plants-are-neat/plants-are-neat.github.io/assets/SerialInit.PNG

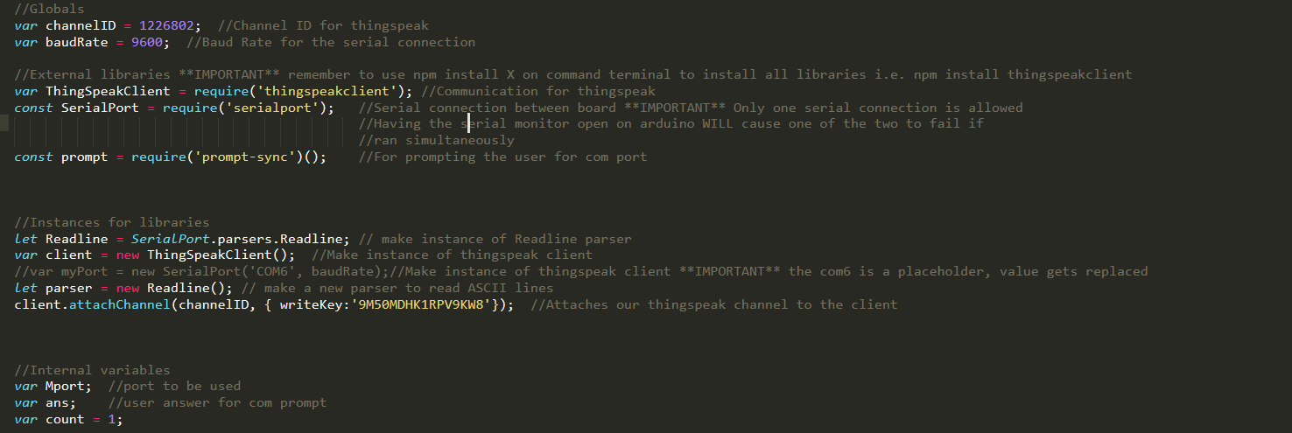
assets/SerialInit.PNG
