plants-are-neat/plants-are-neat.github.io/assets/SerialPrompt.PNG

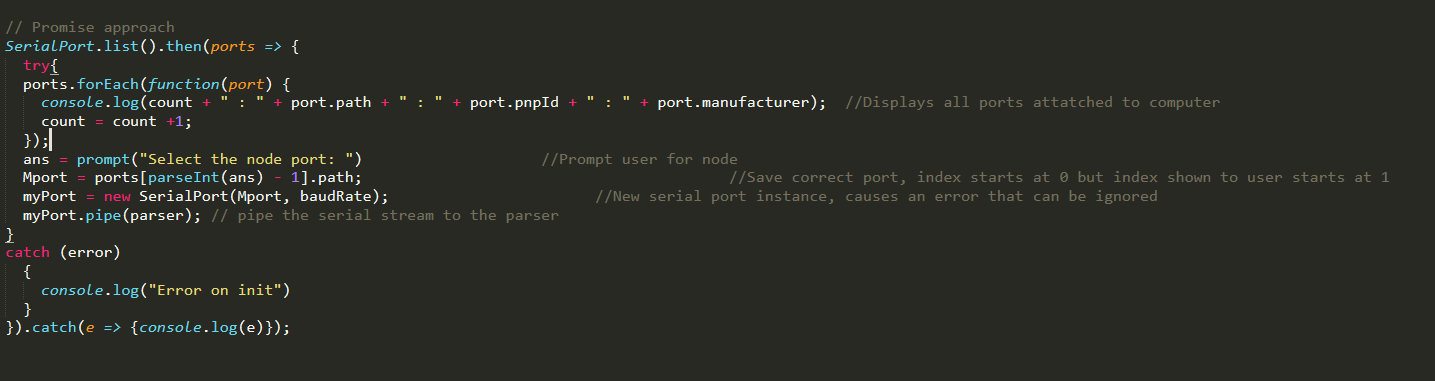
assets/SerialPrompt.PNG
