plants-are-neat/plants-are-neat.github.io/assets/SerialRead.PNG

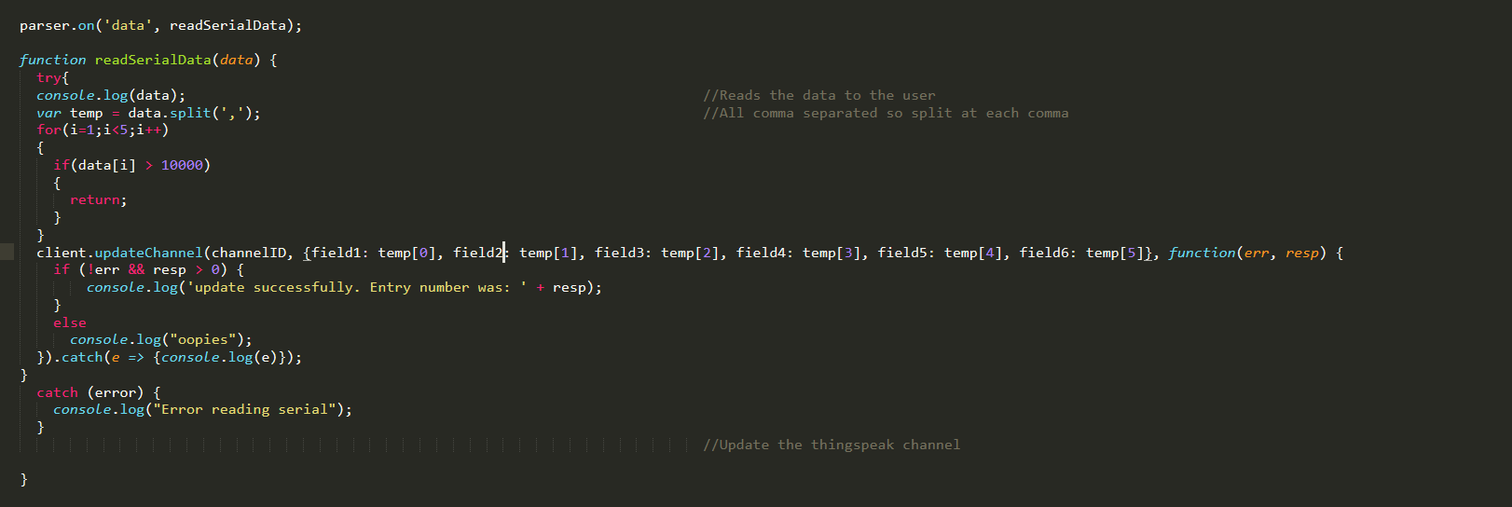
assets/SerialRead.PNG
