plants-are-neat/plants-are-neat.github.io/images/ben.jpg

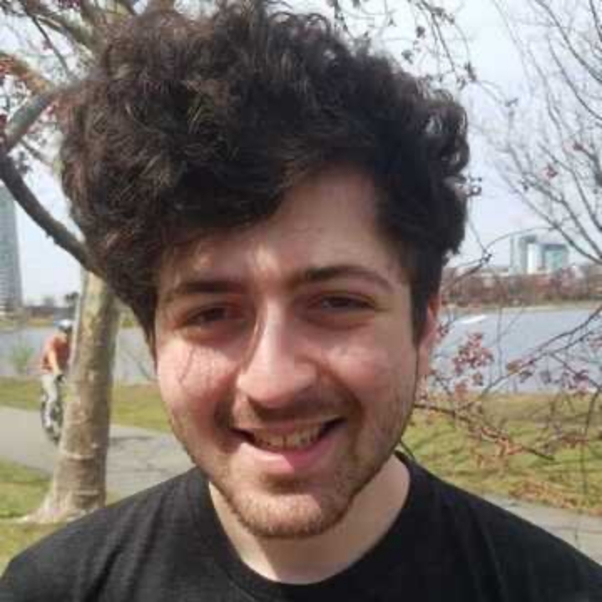
images/ben.jpg
