plants-are-neat/plants-are-neat.github.io/images/img3.jpg

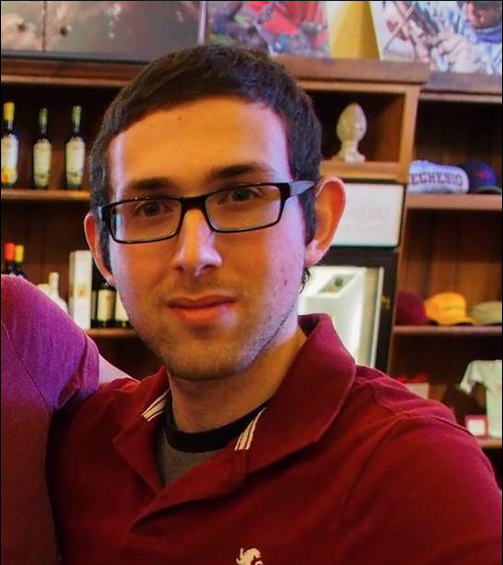
images/img3.jpg
