plants-are-neat/plants-are-neat.github.io/images/img5.jpg

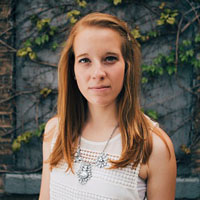
images/img5.jpg
