plants-are-neat/plants-are-neat.github.io/images/maxine.jpg

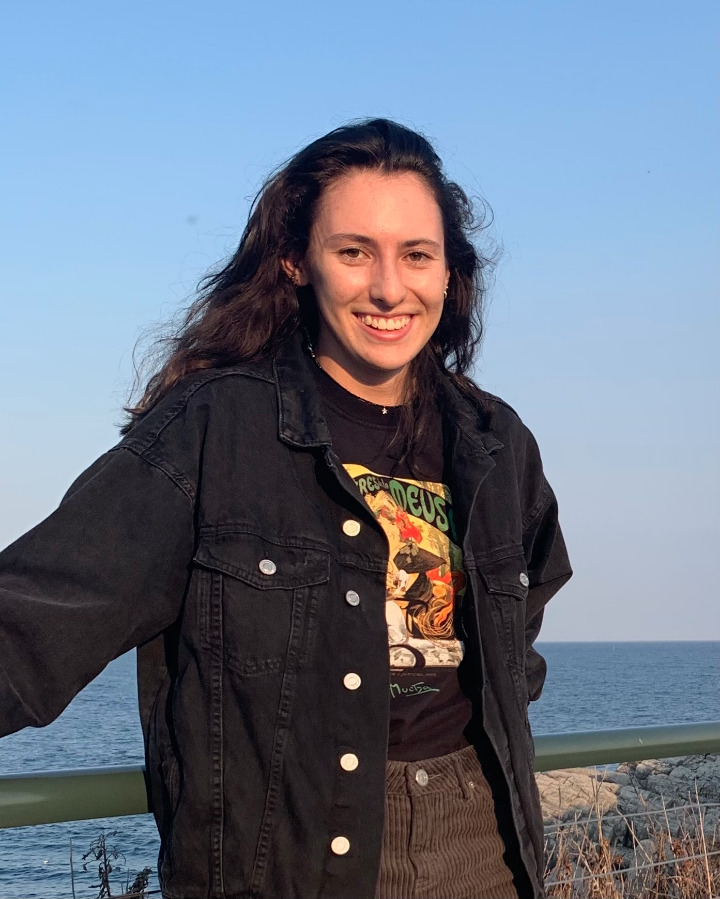
images/maxine.jpg
