plants-are-neat/plants-are-neat.github.io/images/noah.JPG

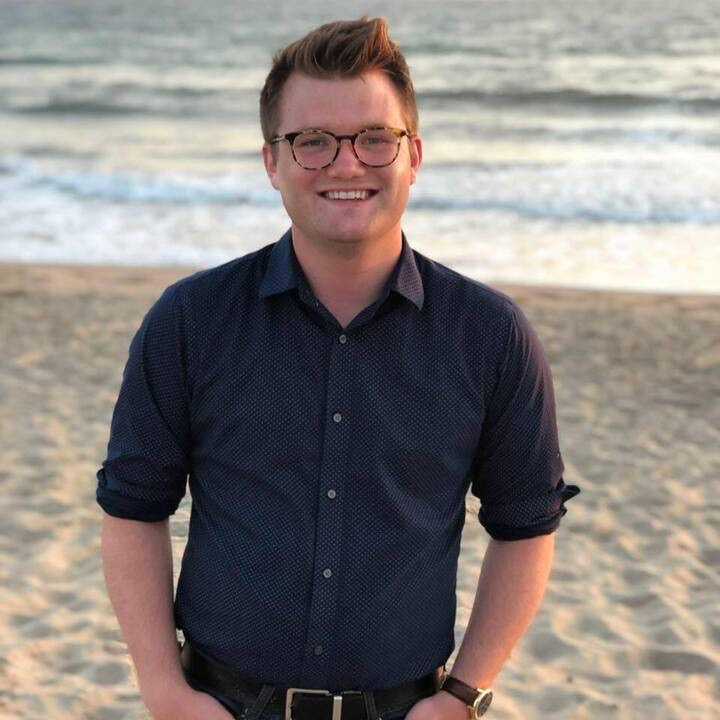
images/noah.JPG
