plants-are-neat/plants-are-neat.github.io/images/sergio.jpg

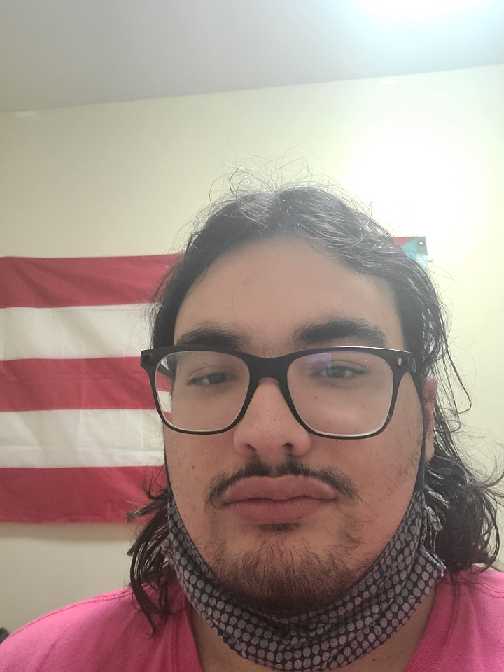
images/sergio.jpg
