plants-are-neat/plants-are-neat.github.io/images/shark.jpg

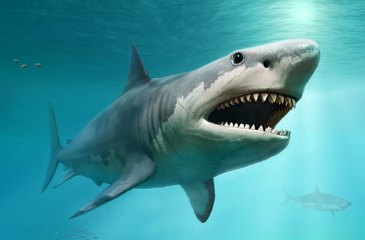
images/shark.jpg
