plants-are-neat/plants-are-neat.github.io/client_node/client_node.ino

// modified from rf22_mesh_server

#define RH_MESH_MAX_MESSAGE_LEN 50
#define RF95_FREQ 915

#include <RHMesh.h>
#include <RH_RF95.h>
#include <RHGenericDriver.h>
#include <RHRouter.h>
#include <SPI.h>

#define CLIENT_ADDRESS 1

#define numServers 4
int SERVERS[numServers];
int counters[numServers];

#define THERM A0
#define RFM95_CS 8
#define RFM95_RST 4
#define RFM95_INT 3

//radio driver
RH_RF95 driver(RFM95_CS, RFM95_INT);

// set up manager
RHMesh manager(driver, CLIENT_ADDRESS);

void setup() 
{
  int i;
  pinMode(RFM95_RST, OUTPUT);
  digitalWrite(RFM95_RST, HIGH);
  Serial.begin(9600);

  for( i = 0; i < numServers; i++) { // Initialise values
    SERVERS[i] = i + 1;
    counters[i] = 0;
  }
  while(!Serial)
  Serial.println(sizeof(SERVERS));
  if (!manager.init())
    Serial.println("init failed");
  while (!driver.init()) {
    Serial.println("LoRa radio init failed");
    Serial.println("Uncomment '#define SERIAL_DEBUG' in RH_RF95.cpp for detailed debug info");
    while (1);
  }
  Serial.println("LoRa radio init OK!");
     
 // Defaults after init are 434.0MHz, modulation GFSK_Rb250Fd250, +13dbM
  if (!driver.setFrequency(RF95_FREQ)) {
   Serial.println("setFrequency failed");
   while (1);
   }
   Serial.print("Set Freq to: "); Serial.println(RF95_FREQ);
   driver.setTxPower(23, false);
}

uint8_t data[] = "Hi, send me the collected data!";
uint8_t buf[RH_MESH_MAX_MESSAGE_LEN];

void loop()
{
  int CURRENT_SERVER, i; // Variable to hold the current server (to loop)
  for(CURRENT_SERVER = 1; CURRENT_SERVER < sizeof(SERVERS)/4; CURRENT_SERVER++)
  {
    for( i = 0; i < RH_MESH_MAX_MESSAGE_LEN; i++)
      buf[i] = 0;
    Serial.print("Sending poll request from server");
    Serial.println(CURRENT_SERVER);
    if (manager.sendtoWait(data, sizeof(data), SERVERS[CURRENT_SERVER]) == RH_ROUTER_ERROR_NONE)
    {
      uint8_t len = sizeof(buf);
      uint8_t from;    
      if (manager.recvfromAckTimeout(buf, &len, 3000, &from)) // Waits 3 seconds for a response
       {
          Serial.print("got reply from : 0x");
          Serial.println(from, HEX);
          Serial.println("The collected data is:");
          Serial.println((char*)buf);
          //Serial.println(driver.lastRssi(),DEC);
       }
      else // Removing the error message
      {
        //Serial.println("No reply, is rf95_mesh_server1, rf95_mesh_server2, rf95_mesh_server3 running?");
      }
   }
   else
    Serial.println("sendtoWait failed. Are the intermediate mesh servers running?");
   delay(3000); // Delay between requesting data from different nodes 

  }
}
