plants-are-neat/plants-are-neat.github.io/Upload Codes/WriteMultipleFields/secrets.h

// Use this file to store all of the private credentials 
// and connection details

#define SECRET_SSID "BigBlind"    // replace MySSID with your WiFi network name
#define SECRET_PASS "Fantastic" // replace MyPassword with your WiFi password

#define SECRET_CH_ID 1310790      // replace 0000000 with your channel number
#define SECRET_WRITE_APIKEY "US1U1HBGB67KI4FK"   // replace XYZ with your channel write API Key
